ElectronicCats/badge-44con-2025/firmware/spritebank.h

//          >>>>>  T-I-N-Y  P-A-C-M-A-N for ATTINY85  GPL v3 <<<<
//                   Programmer: Daniel C 2018-2021
//             Contact EMAIL: electro_l.i.b@tinyjoypad.com
//           https://sites.google.com/view/arduino-collection

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
//  2023 modified to work with CH32V003 by Stefan Wagner: github.com/wagiminator.

#pragma once

#include "ch32fun.h"

#ifdef __cplusplus
extern "C" {
#endif

typedef struct PERSONAGE{
uint8_t anim;
uint8_t guber;
uint8_t type;
uint8_t DirectionAnim;
uint8_t DirectionH;
uint8_t DirectionV;
uint8_t x;
uint8_t Decalagey;
int8_t y;
uint8_t switchanim;
}PERSONAGE;

const uint8_t  Music [] = {
125,255,125,255,110,255,110,255,95,255,95,255,75,255,75,255,75,255,116,255,116,255,116,255,116,
255,100,255,100,255,100,255,100,255,125,255,125,255,125,255,125,255,115,255,115,255,125,255,125,
255,140,255,140,255,120,255,120,255,100,255,100,255,100,255,125,255,125,255,125,255,125,255,115,
255,115,255,125,255,125,255,140,255,140,255,115,255,115,255,125,255,125,255,140,255,140,255,155,
255,155,255,155,255,165,255,165,255,165,255,170,255,170,255,170,255,170,255,170,255,165,255,165,
255,165,255,165,255,165,255,165,255,170,255,170,255,170,255,170,255,170,255};

const uint8_t  fruits [] = {
0x60, 0xF6, 0xFF, 0x6F, 0x46, 0x58, 0xF0, 0xC0, 0x1C, 0x36, 0x3F, 0x5F, 0x77, 0x3F, 0x1E, 0x3B,
0x38, 0x6C, 0x5C, 0x7C, 0x38, 0x38, 0x10, 0x60, 0x1F, 0x7E, 0x58, 0xB0, 0xE0, 0xE0, 0x40, 0x40
};

const uint8_t caracters []  = {
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
    0xff, 0xff, 0xff, 0xff, 0xff, 0xff, 0xff, 0xff, 0xff, 0x00, 0xe1, 0xed, 0x6d, 0x6d, 0x6d, 0x6c, 
    0x6c, 0x6c, 0x6c, 0x6d, 0x6d, 0xed, 0xed, 0xe1, 0x00, 0xe1, 0x6d, 0x6c, 0x00, 0xff, 0xff, 0xff, 
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
};

#ifdef __cplusplus
};
#endif
