ElectronicCats/badge-44con-2025/firmware/oled_min.h

// ===================================================================================
// SSD1306 128x64 Pixels OLED Minimal Functions                               * v1.0 *
// ===================================================================================
//
// Collection of the most necessary functions for controlling an SSD1306 128x64 pixels
// I2C OLED.
//
// References:
// -----------
// - TinyOLEDdemo: https://github.com/wagiminator/attiny13-tinyoleddemo
// - Neven Boyanov: https://github.com/tinusaur/ssd1306xled
// - Stephen Denne: https://github.com/datacute/Tiny4kOLED
//
// 2022 by Stefan Wagner: https://github.com/wagiminator

#pragma once

#ifdef __cplusplus
extern "C" {
#endif

#include "i2c_tx.h"

// OLED definitions
#define OLED_ADDR         0x78    // OLED write address (0x3C << 1)
#define OLED_CMD_MODE     0x00    // set command mode
#define OLED_DAT_MODE     0x40    // set data mode

// OLED commands
#define OLED_COLUMN_LOW   0x00    // set lower 4 bits of start column (0x00 - 0x0F)
#define OLED_COLUMN_HIGH  0x10    // set higher 4 bits of start column (0x10 - 0x1F)
#define OLED_MEMORYMODE   0x20    // set memory addressing mode (following byte)
#define OLED_COLUMNS      0x21    // set start and end column (following 2 bytes)
#define OLED_PAGES        0x22    // set start and end page (following 2 bytes)
#define OLED_SCROLL_OFF   0x2E    // deactivate scroll command
#define OLED_STARTLINE    0x40    // set display start line (0x40-0x7F = 0-63)
#define OLED_CONTRAST     0x81    // set display contrast (following byte)
#define OLED_CHARGEPUMP   0x8D    // (following byte - 0x14:enable, 0x10: disable)
#define OLED_XFLIP_OFF    0xA0    // don't flip display horizontally
#define OLED_XFLIP        0xA1    // flip display horizontally
#define OLED_INVERT_OFF   0xA6    // set non-inverted display
#define OLED_INVERT       0xA7    // set inverse display
#define OLED_MULTIPLEX    0xA8    // set multiplex ratio (following byte)
#define OLED_DISPLAY_OFF  0xAE    // set display off (sleep mode)
#define OLED_DISPLAY_ON   0xAF    // set display on
#define OLED_PAGE         0xB0    // set start page (following byte)
#define OLED_YFLIP_OFF    0xC0    // don't flip display vertically
#define OLED_YFLIP        0xC8    // flip display vertically
#define OLED_OFFSET       0xD3    // set display offset (y-scroll: following byte)
#define OLED_COMPINS      0xDA    // set COM pin config (following byte)

// Macros
#define OLED_xfer_start     I2C_start(OLED_ADDR)
#define OLED_xfer_stop      I2C_stop
#define OLED_send_byte(b)   I2C_write(b)
#define OLED_data_stop      I2C_stop
#define OLED_command_stop   I2C_stop


// OLED initialisation sequence
const uint8_t OLED_INIT_CMD[] = {
  OLED_MULTIPLEX,   0x3F,                 // set multiplex ratio  
  OLED_CHARGEPUMP,  0x14,                 // set DC-DC enable  
  OLED_MEMORYMODE,  0x00,                 // set horizontal addressing mode
  OLED_COLUMNS,     0x00, 0x7F,           // set start and end column
  OLED_PAGES,       0x00, 0x3F,           // set start and end page
  OLED_COMPINS,     0x12,                 // set com pins
  OLED_XFLIP, OLED_YFLIP,                 // flip screen
  OLED_DISPLAY_ON                         // display on
};

// OLED init function
void OLED_init(void) {
  uint8_t i;
  I2C_init();                             // initialize I2C first
  I2C_start(OLED_ADDR);                   // start transmission to OLED
  I2C_write(OLED_CMD_MODE);               // set command mode
  for(i = 0; i < sizeof(OLED_INIT_CMD); i++)
    I2C_write(OLED_INIT_CMD[i]);          // send the command bytes
  I2C_stop();                             // stop transmission
}

// Start sending data
void OLED_data_start(void) {
  I2C_start(OLED_ADDR);                   // start transmission to OLED
  I2C_write(OLED_DAT_MODE);               // set data mode
}

// Start sending command
void OLED_command_start(void) {
  I2C_start(OLED_ADDR);                   // start transmission to OLED
  I2C_write(OLED_CMD_MODE);               // set command mode
}

// OLED send command
void OLED_send_command(uint8_t cmd) {
  I2C_start(OLED_ADDR);                   // start transmission to OLED
  I2C_write(OLED_CMD_MODE);               // set command mode
  I2C_write(cmd);                         // send command
  I2C_stop();                             // stop transmission
}

// OLED set cursor position
void OLED_setpos(uint8_t x, uint8_t y) {
  I2C_start(OLED_ADDR);                   // start transmission to OLED
  I2C_write(OLED_CMD_MODE);               // set command mode
  I2C_write(OLED_PAGE | y);	              // set page start address
  I2C_write(x & 0x0F);			              // set lower nibble of start column
  I2C_write(OLED_COLUMN_HIGH | (x >> 4)); // set higher nibble of start column
  I2C_stop();                             // stop transmission
}

// OLED fill screen
void OLED_fill(uint8_t p) {
  OLED_setpos(0, 0);                      // set cursor to display start
  I2C_start(OLED_ADDR);                   // start transmission to OLED
  I2C_write(OLED_DAT_MODE);               // set data mode
  for(uint16_t i=128*8; i; i--) I2C_write(p); // send pattern
  I2C_stop();                             // stop transmission
}

// OLED draw bitmap
void OLED_draw_bmp(uint8_t x0, uint8_t y0, uint8_t x1, uint8_t y1, const uint8_t* bmp) {
  for(uint8_t y = y0; y < y1; y++) {
    OLED_setpos(x0, y);
    I2C_start(OLED_ADDR);
    I2C_write(OLED_DAT_MODE);
    for(uint8_t x = x0; x < x1; x++)
      I2C_write(*bmp++);
    I2C_stop();
  }
}

#ifdef __cplusplus
};
#endif
